kd4cbm/EngModem-Mini/enclosure/renders/rear_panel_layout.png

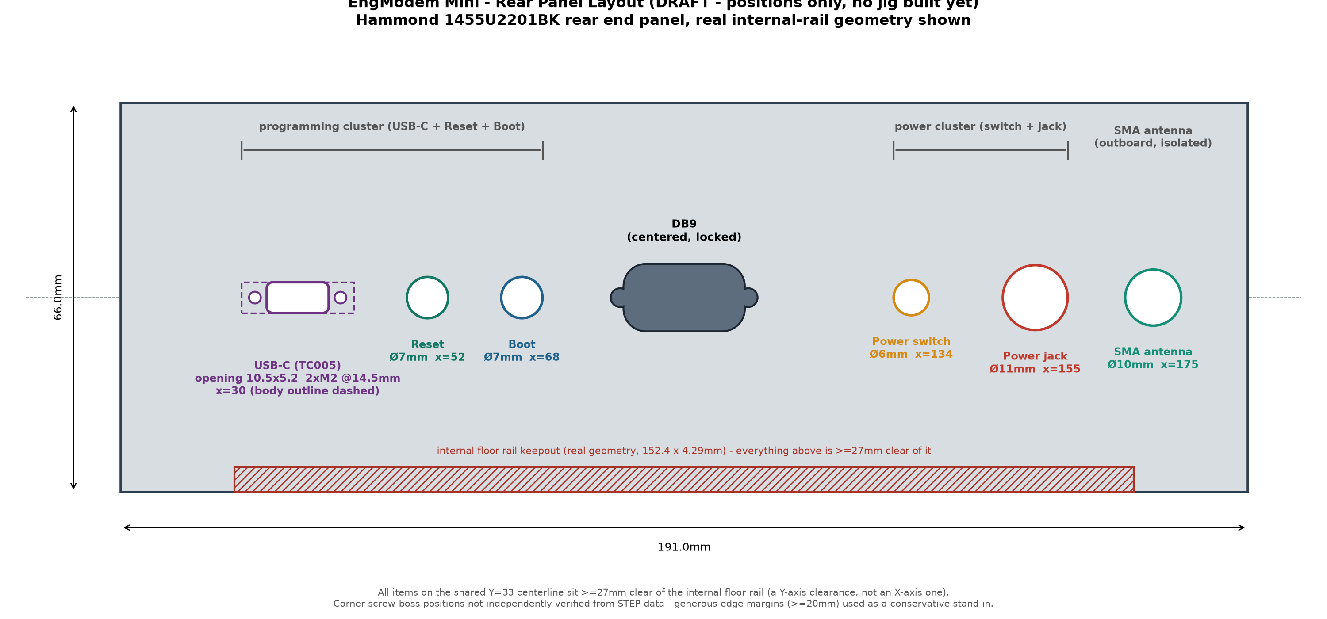
enclosure/renders/rear_panel_layout.png
